oholsen/hagedag/control/simulation/fill.png

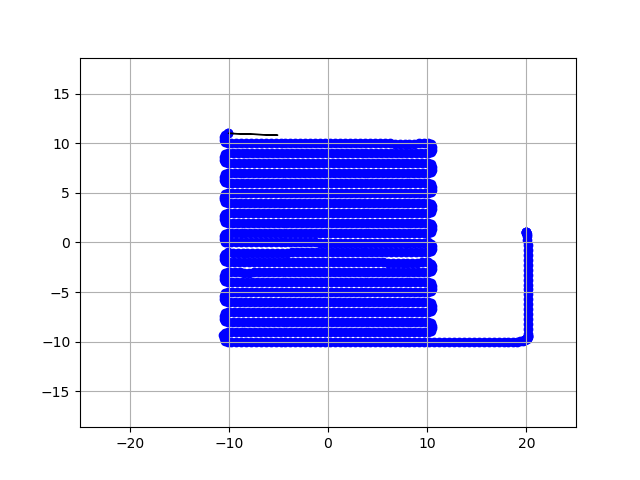
control/simulation/fill.png
